signalius/RFAmplifier_GALI-84/doc/Teko 371.16.pdf

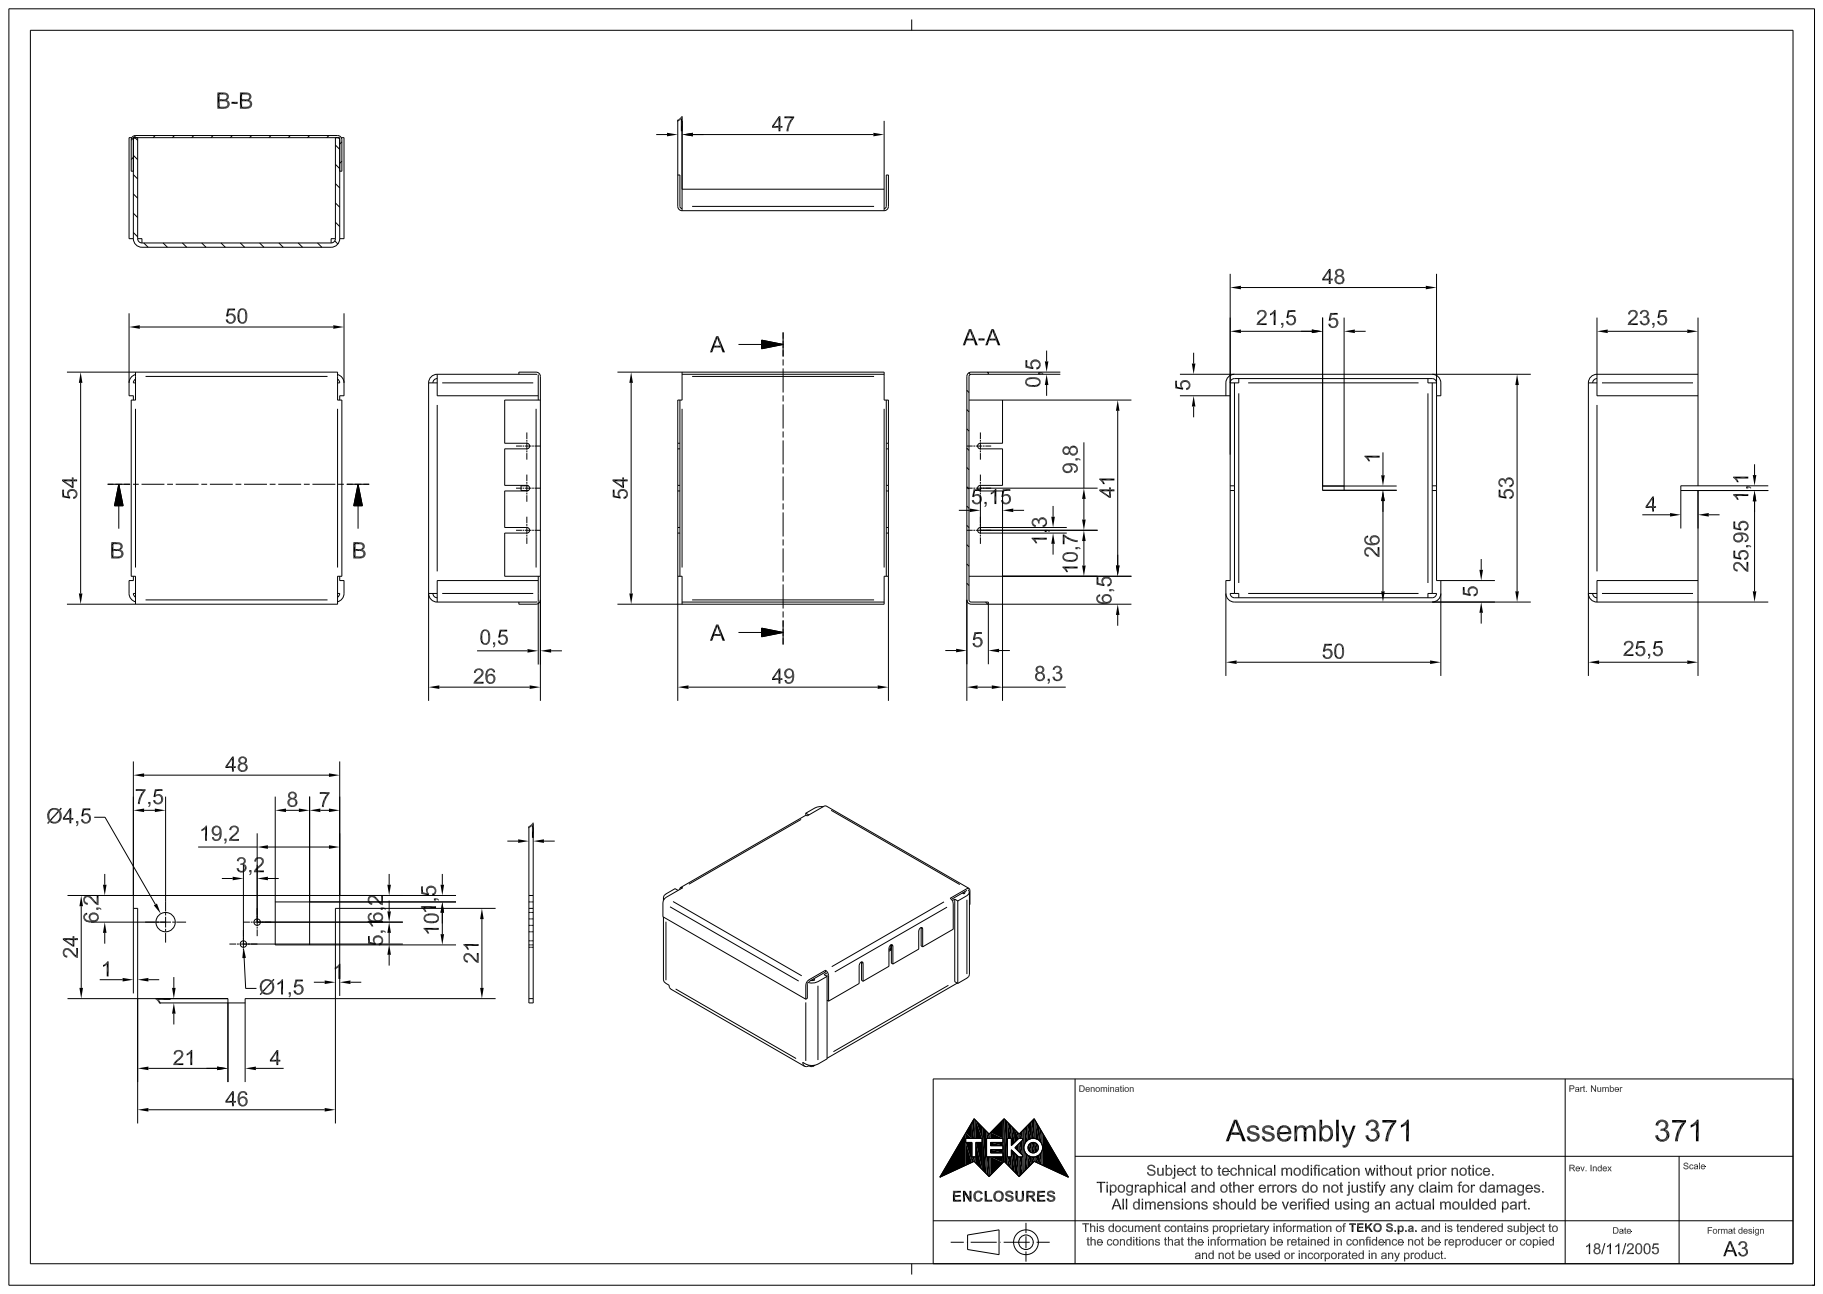
[picture p8: page 1]
